invisibleFlock/Open-Field-Recorder/hardware/Bottom layer.png

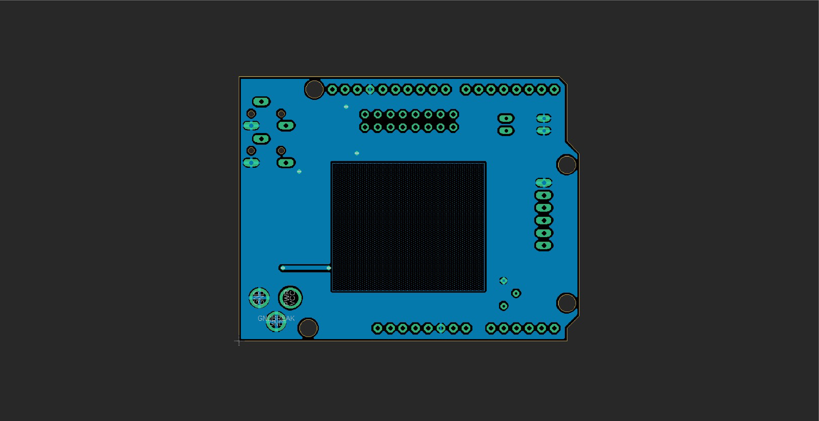
hardware/Bottom layer.png
