invisibleFlock/Open-Field-Recorder/hardware/Images/Render.png

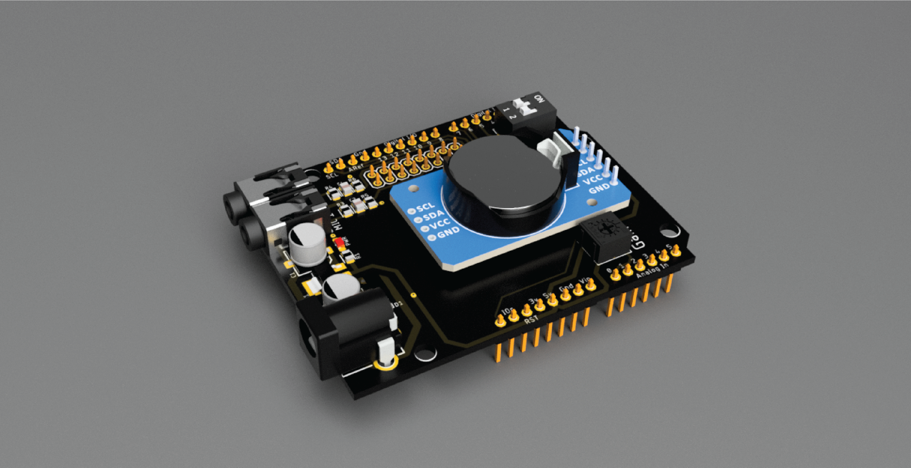
hardware/Images/Render.png
