invisibleFlock/Open-Field-Recorder/hardware/Images/Side.png

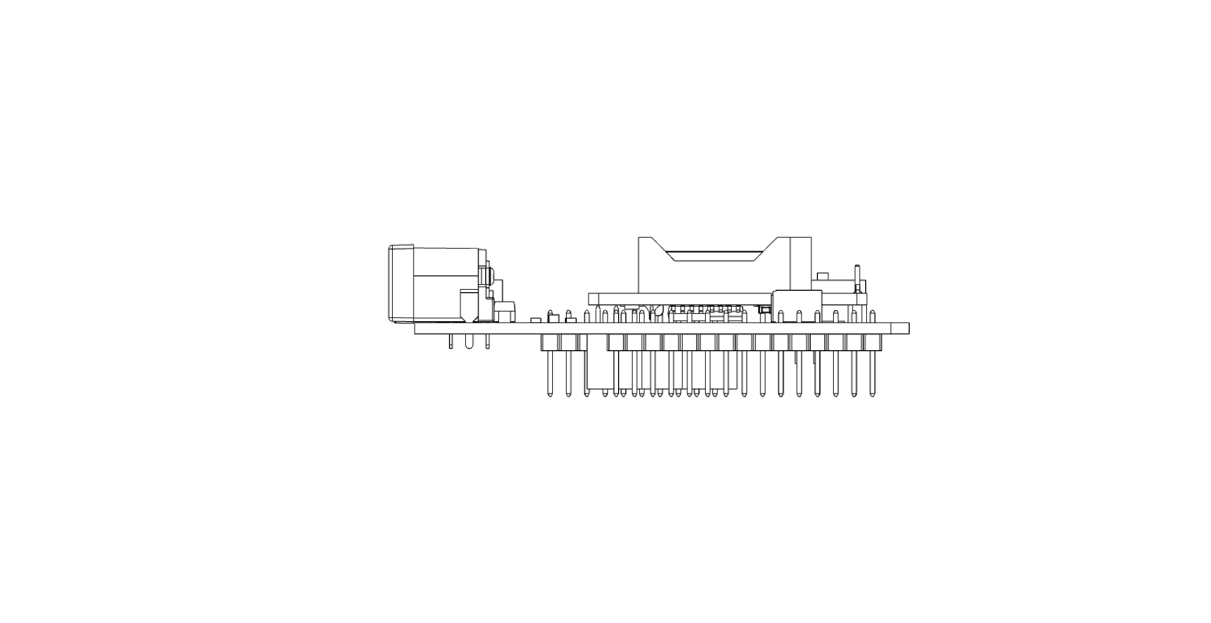
hardware/Images/Side.png
