invisibleFlock/Open-Field-Recorder/hardware/Screen and Mask.png

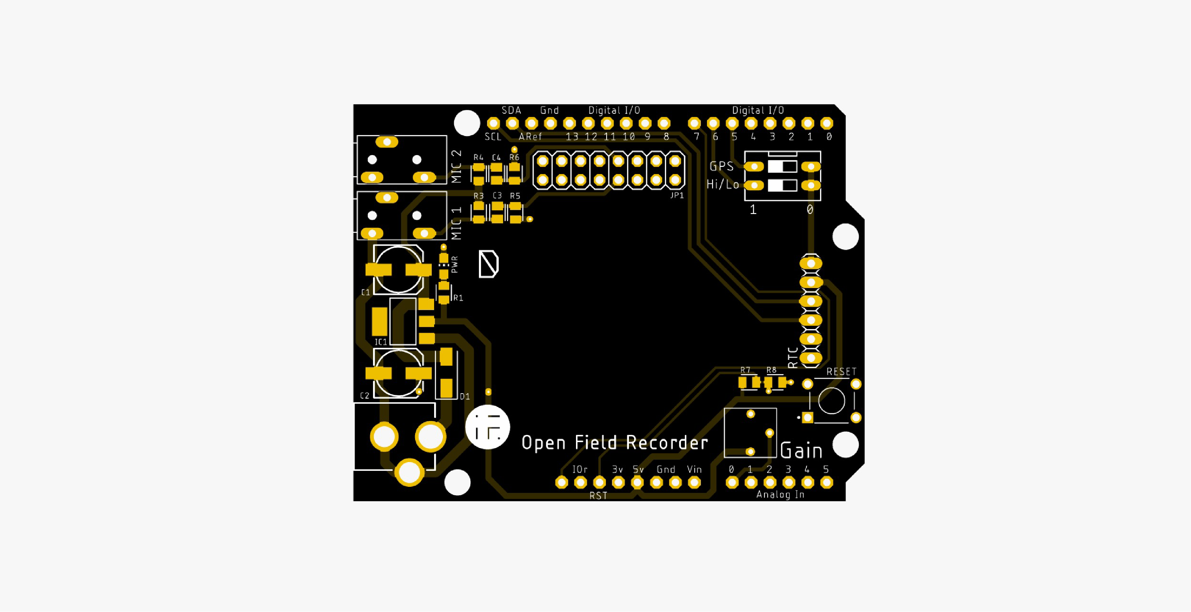
hardware/Screen and Mask.png
