invisibleFlock/Open-Field-Recorder/hardware/Top layer.png

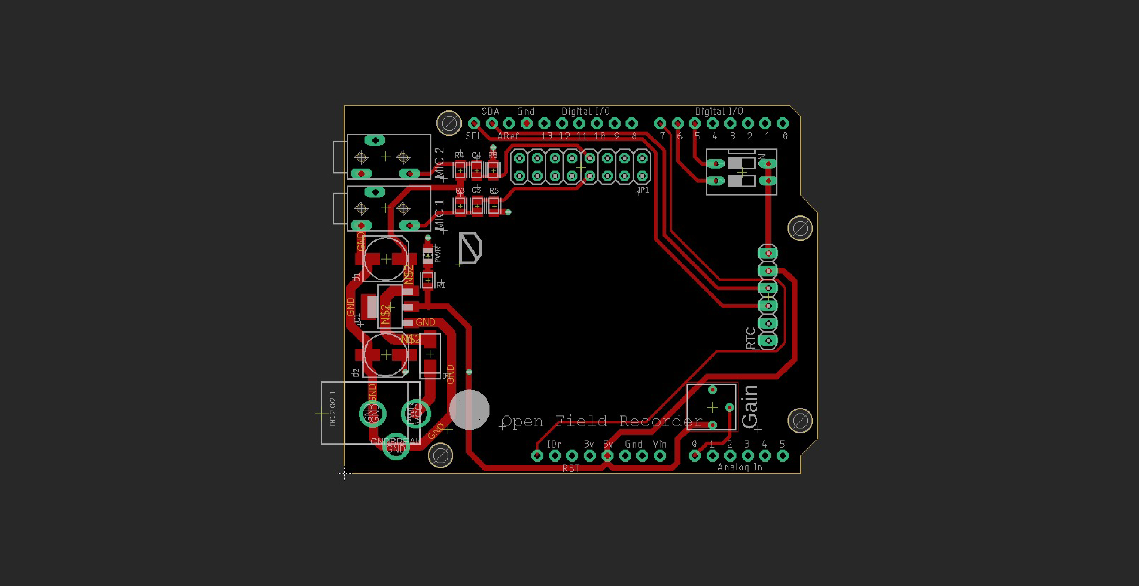
hardware/Top layer.png
